ropg/hyper-pi/case/images/bottom-half_1.jpg

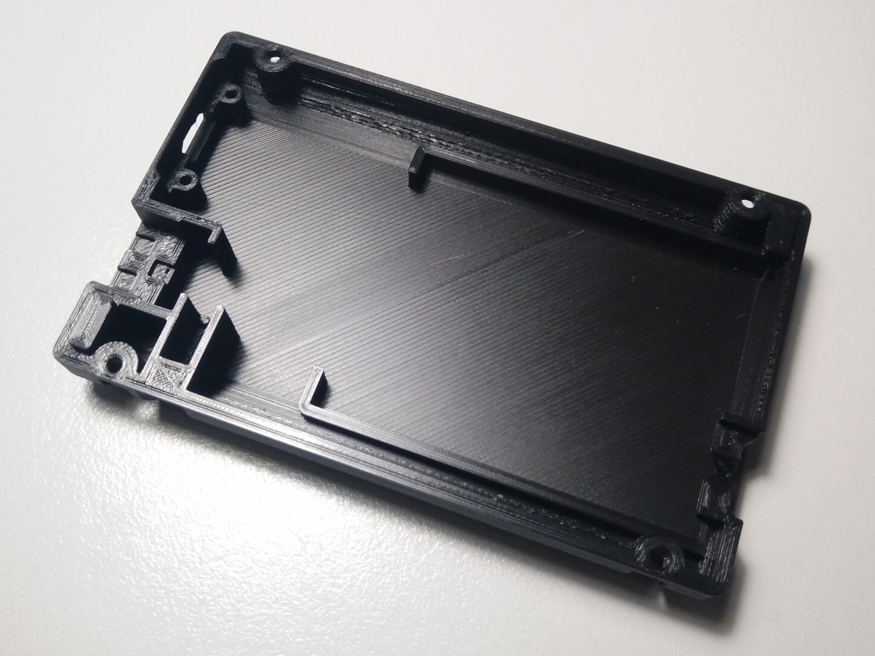
case/images/bottom-half_1.jpg
