ropg/hyper-pi/case/images/bottom-half_2.jpg

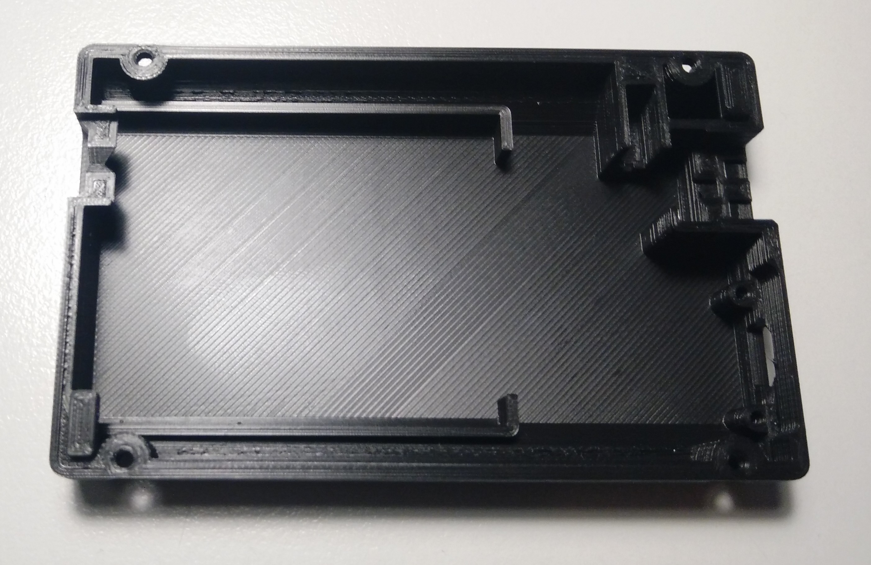
case/images/bottom-half_2.jpg
