ropg/hyper-pi/case/images/display.jpg

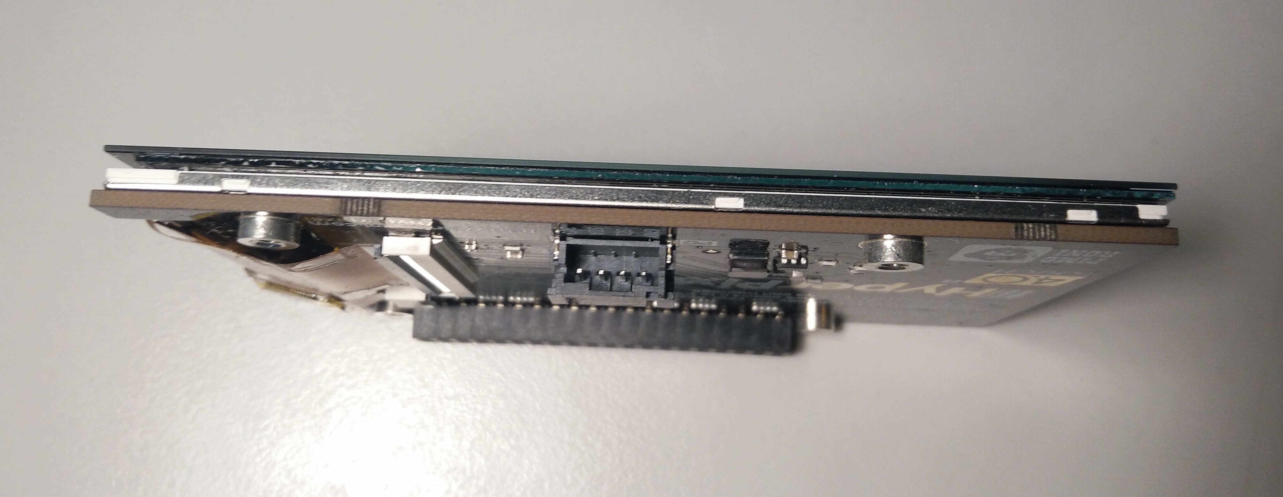
case/images/display.jpg
