ropg/hyper-pi/case/images/microSD-extender_2.jpg

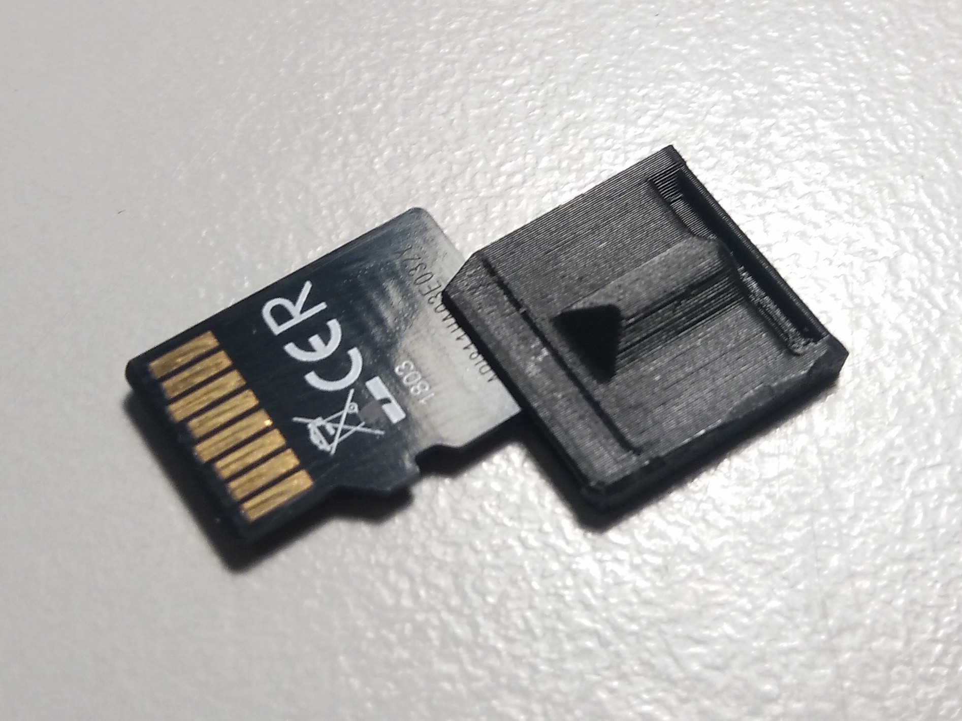
case/images/microSD-extender_2.jpg
