ropg/hyper-pi/case/images/microSD-slot.jpg

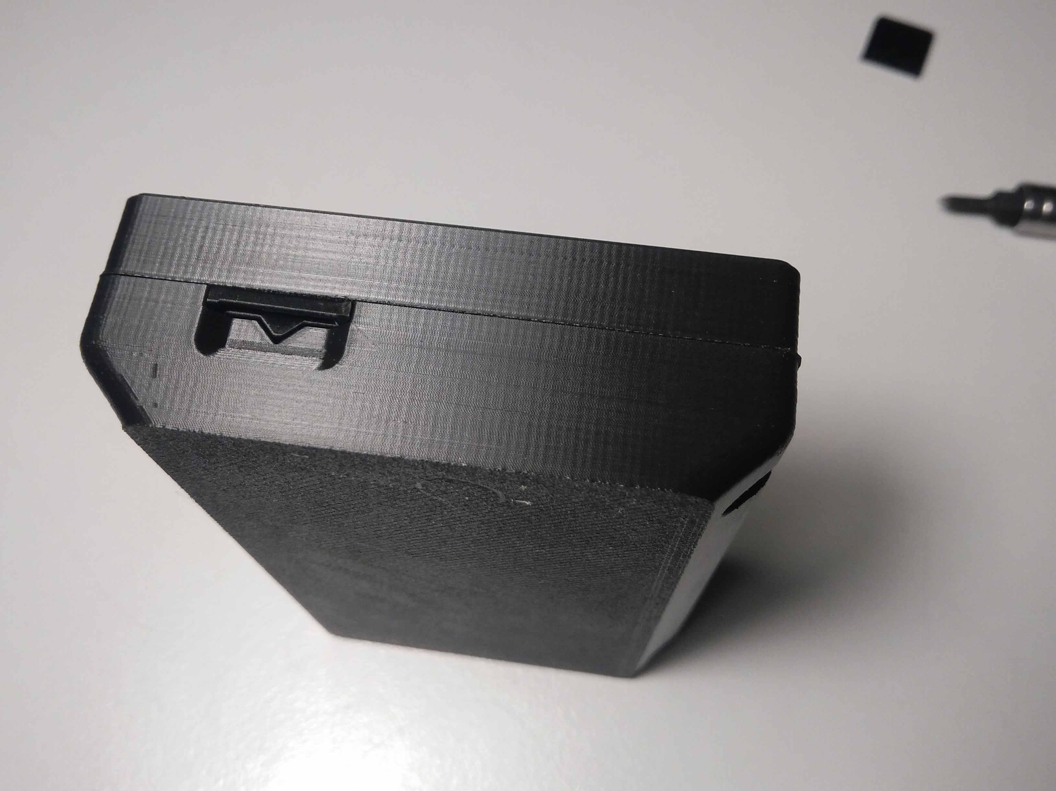
case/images/microSD-slot.jpg
