ropg/hyper-pi/case/images/top-half+display.jpg

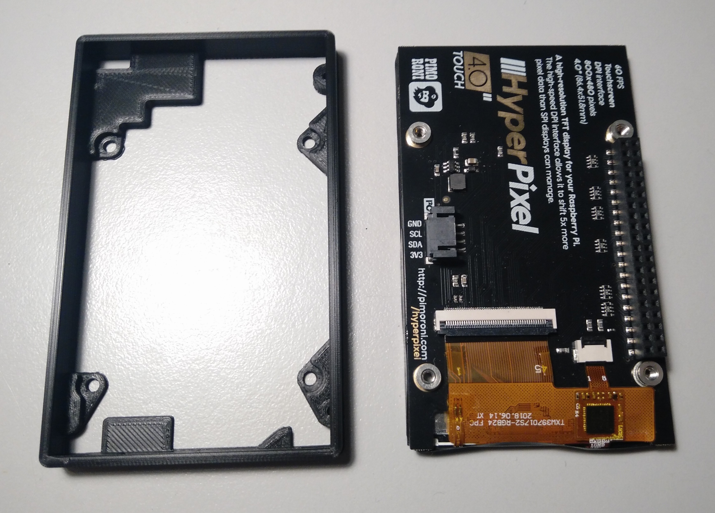
case/images/top-half+display.jpg
