ropg/hyper-pi/case/images/USB_pins.jpg

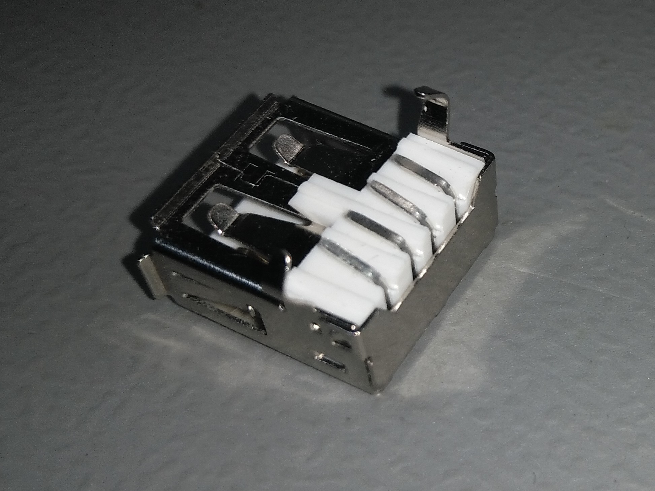
case/images/USB_pins.jpg
