ropg/hyper-pi/case/images/bottom-half_assembly_1.jpg

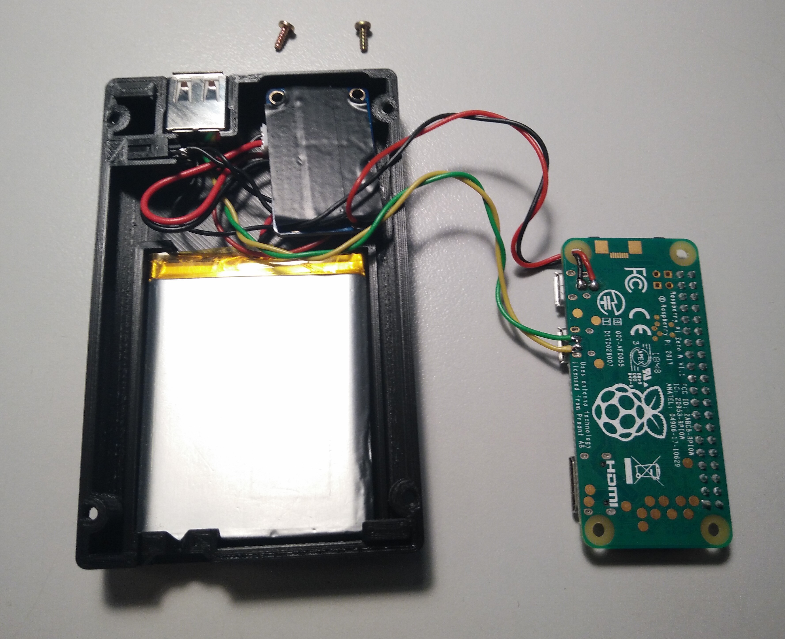
case/images/bottom-half_assembly_1.jpg
