ropg/hyper-pi/case/images/bottom-half_assembly_3.jpg

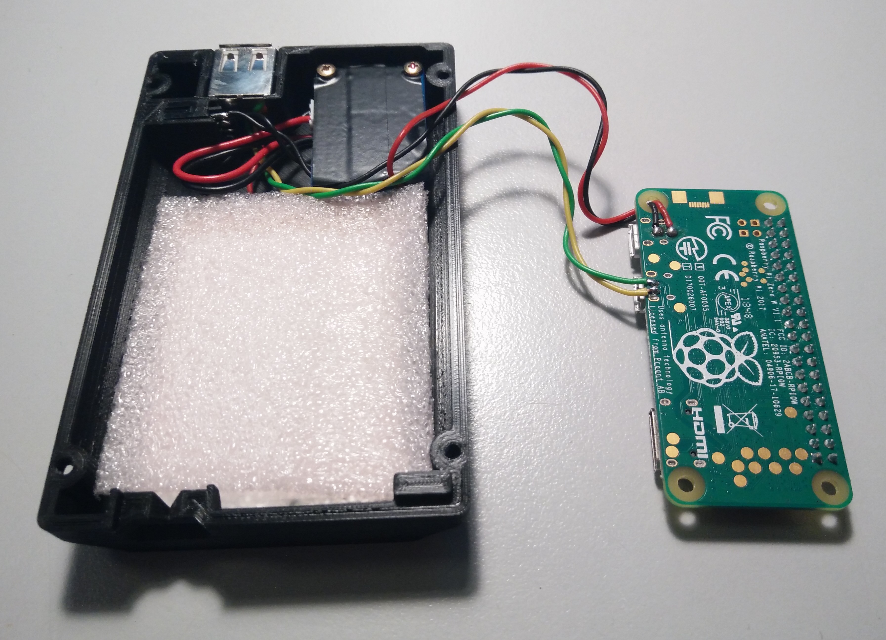
case/images/bottom-half_assembly_3.jpg
