ropg/hyper-pi/case/images/components_wiring.jpg

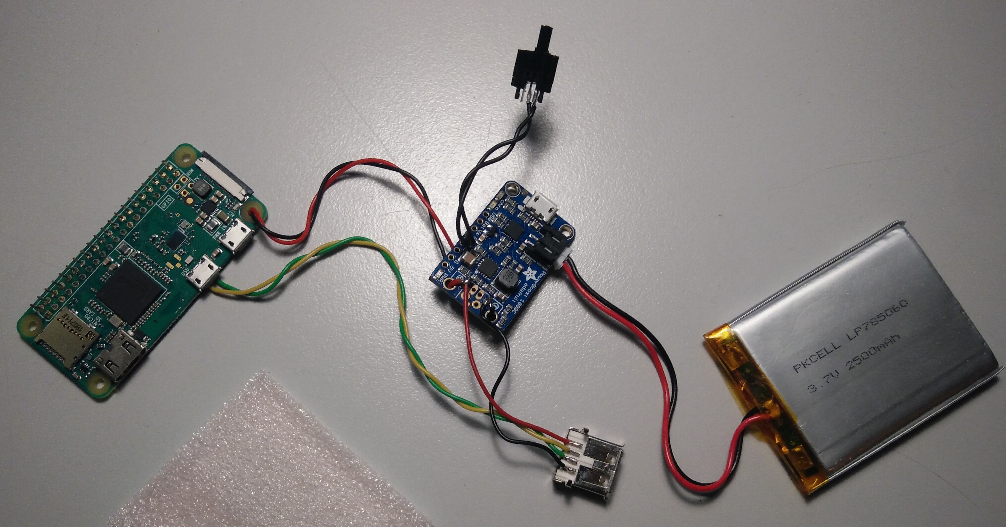
case/images/components_wiring.jpg
