ropg/hyper-pi/case/images/printing.jpg

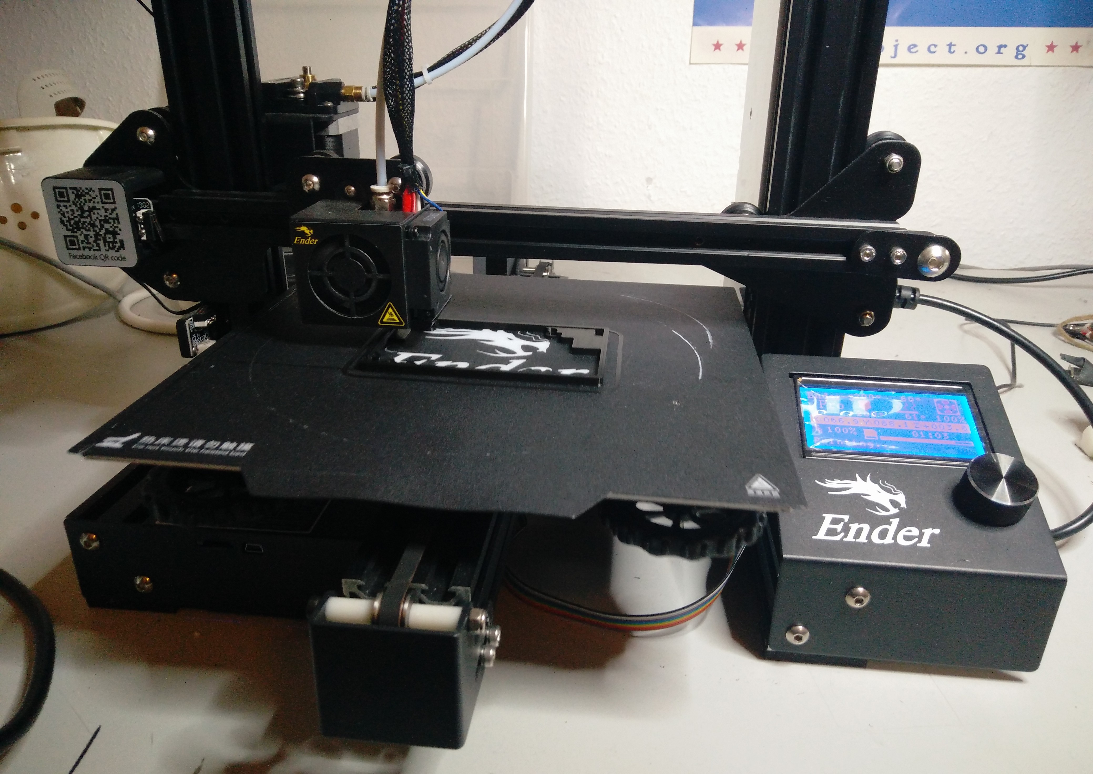
case/images/printing.jpg
