ropg/hyper-pi/case/images/top+bottom_assembly_1.jpg

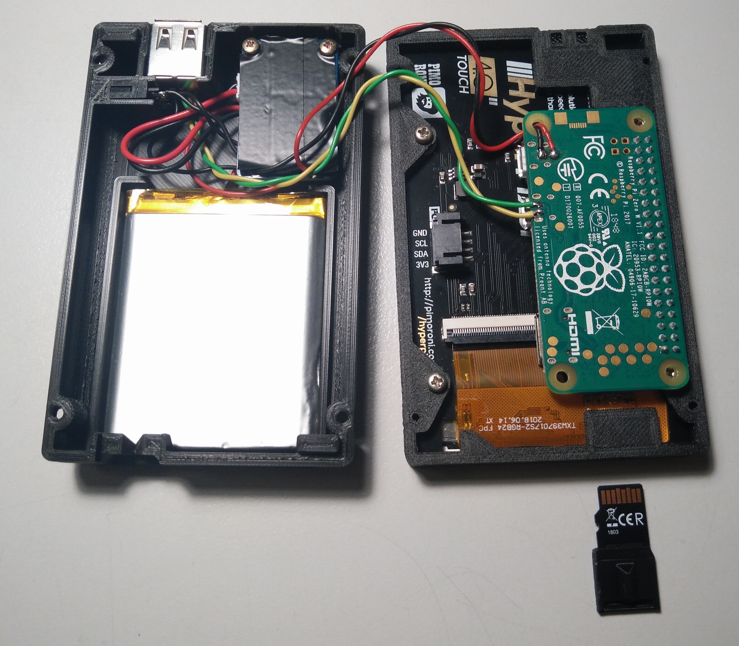
case/images/top+bottom_assembly_1.jpg
