ropg/hyper-pi/case/images/top+bottom_assembly_2.jpg

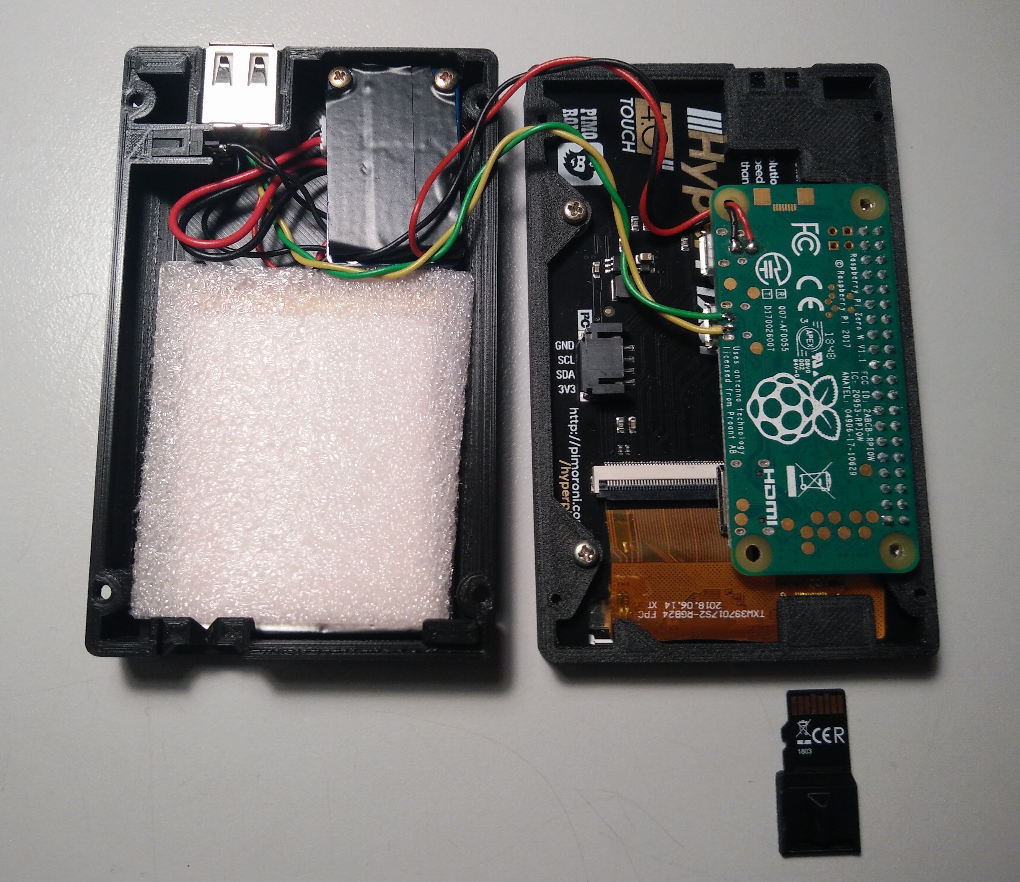
case/images/top+bottom_assembly_2.jpg
