ropg/hyper-pi/case/images/top-half+display_assembled.jpg

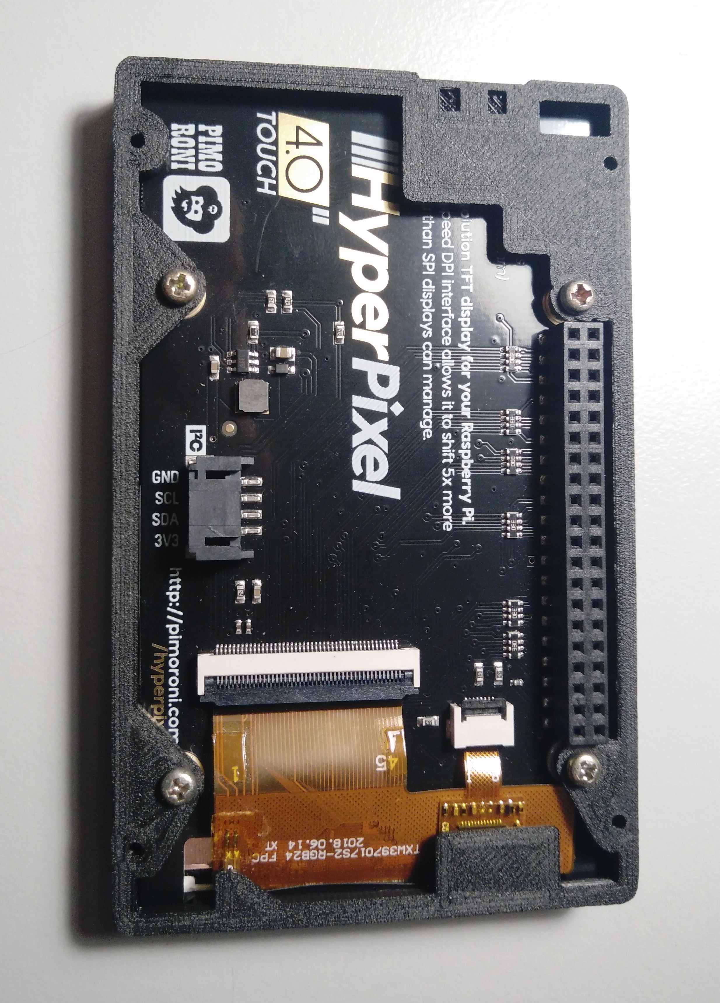
case/images/top-half+display_assembled.jpg
